JVKran/Taguino/Master/Boundary/HCSR04/main.cpp

#include "hwlib.hpp"
#include "HCSR04.hpp"

int main(){
   	auto triggerPin = hwlib::target::pin_out(hwlib::target::pins::d8);
   	auto echoPin = hwlib::target::pin_in(hwlib::target::pins::d9);
	auto distanceSensor = HCSR04(triggerPin, echoPin);

	//Wait for terminal
	hwlib::wait_ms(500);

	for(;;){
		hwlib::cout << "Distance: " << hwlib::setw(5) << distanceSensor.getDistance() << hwlib::endl;
		hwlib::wait_ms(1000);
	}
}
