JVKran/Taguino/Master/Boundary/Mp3/mp3.hpp

///@file
#ifndef _MP3_HPP
#define _MP3_HPP

#include <array>
#include "hwlib.hpp"
/// \brief
/// This sounds class has a template "<int, N>" and an array called sound where songs are put in.
/// \details
/// The Array holds N amount of ints, these ints are used to play a song.
/// This class has 3 functions:
///		- play(int i): 	The play function returns the given sound on its position.	
///		- size(): 		The size function returns the size of the sound array.
///		- set(): 		The set function sets the given value.

template< int N >
class sounds{
private:
	std::array< int, N > sound;
public:
/// \brief
/// Function to return from array sound.
/// \details
/// This function is used to return a value from sound at position i - 1.
	int play( int i ){ return sound[ i-1 ]; }
/// \brief
/// Function to return size of sound.
/// \details
/// This function returns the size of the sound array.
	int size(){ return sound.size();}
/// \brief
///	Function to set a sound.
/// \details
/// This function will set the given value at a new position.
	void set( int setSound ){ sound[setSound-1] = setSound; }

};

class hwuart{
	//Usart * hw_usart = USART0;
	public:
	hwuart();
	bool usart_char_available();
	char usart_getc();
	void usart_putc(char c);
};

/// \brief
///	The class send inherits from hwuart and is used to send commands to the mp3 module.
/// \details
///	The class has one function:
/// 	- executeCMD( uint8_t CMD, uint8_t par1, uint8_t par2): 
///     	This needs the mp3 command, command specific value, command specific value2 and will then send commands to the mp3 module.
class send : public hwuart{
public:
/// \brief
///	Function to execute commands to the mp3 module
/// \details
/// This needs the mp3 command, folder and mp3 file. It will send commands to the mp3 module.
	void executeCMD( uint8_t CMD, uint8_t par1, uint8_t par2);
};

/// \brief
///	The mp3 class inherits from send and is used to specify which commands need to be sent
/// \details
///	The class has 5 function:
/// 	- sendCMD(uint8_t CMD, uint8_t par1, uint8_t par2): Send your own commands.
/// 	- resetModule(): 			Reset the mp3 module.
/// 	- playSound( int sound ): 	Play the given sound.
/// 	- pauseSound(): 			Pause the sound.
/// 	- setVolume( int volume ): 	Set the volume.
class mp3 : public send{
public:
/// \brief
/// sendCMD sends your own commands.
/// \details
/// This function will send the command, command specific value, command specific value2 and executes it at the mp3 module.
	void sendCMD( uint8_t CMD, uint8_t par1, uint8_t par2 );
/// \brief
/// resetModule will reset the mp3 module.
/// \details
/// This function will send the command to reset to the mp3 module, 
/// clearing every command you have given to the module.
	void resetModule();
/// \brief
/// playSound will play the given sound.
/// \details
///	This function will send the command to play the given sound from the beginning.
/// Folders on the SD are numbered from 1-99 and mp3 files are numbered from 1 - 255, 
/// giving those values will play the corresponding sound. In this case the folder is always the first one.
	void playSound( int sound );
/// \brief
/// pauseSound will pause the current sound.
/// \details
/// This function will pause the sound that is currently playing,
/// altough there is no start function, meaning this can also be seen as stopping a sound.
	void pauseSound();
/// \brief
/// setVolume will set the volume at given value.
/// \details
/// This function will set the volume of the mp3 module at the given value,
/// the volume can go from 0 - 30.
	void setVolume( int volume ); //Van 0-30
};


/// \brief
/// The mp3Control class inherits mp3 and sounds<N>, it has a template "<int N>" and is used to play songs for given data in NRF
/// \details
/// This initializes the sound array and has 1 function:
/// 	- startPlayingSound(int data): If data is in the sound array, play it.

template< int N >
class mp3Control : public mp3, public sounds<N>{
private:
	int JAZZ=1; int ACTION=2; 
	std::array< int, N > soundTmp = { JAZZ, ACTION };
	sounds<N> sound;
public:
	mp3Control()
	{
		for( const auto &s : soundTmp){
			sound.set(s);
		}
	}
/// \brief
/// startPlayingSound will play a sound corresponding to the given data.
/// \details
/// This function will compare the data to the values in the array, if they are the same it will play the corresponding sound.
	void startPlayingSound( int data ){
		for( int i=1; i<sound.size()+1; i++){ 
			if( data == i ){ 			// If data is a song, play it. +1 because .play will return value -1;
				playSound( sound.play( i ) );
				break;
			}
		}
	}
};

#endif //MP3_HPP
