JVKran/Taguino/Master/Boundary/NRF/NRF24_register.hpp

// File      : NRF24_register.hpp
// Part of   : NRF24L01+ library
// Copyright : menno.vanderjagt@student.hu.nl 2019
//
// Distributed under the Boost Software License, Version 1.0.
// (See accompanying file LICENSE_1_0.txt or copy at 
// http://www.boost.org/LICENSE_1_0.txt)

//commando's
#define R_REGISTER           0x00        //Leest commando en status registers, 5 bit register map address
#define W_REGISTER           0x20        //Schrijft commando en status registers, 5 bit register map address. Uitvoerbaar in power down
#define R_RX_PAYLOAD         0x61        //Leest de RX-payload: 1 - 32 bytes
#define W_TX_PAYLOAD         0xA0        //Schrijft TX-payload 1 - 32 bytes
#define FLUSH_TX             0xE1        //Flush TX FIFO, in TX mode
#define FLUSH_RX             0xE2        //Flush RX FIFO, in RX mode
#define REUSE_TX_PL          0xE3        //Wordt gebruikt voor PTX apparaten, hergebruik laatst verstuurde payload
#define R_RX_PL_WID          0x60        //Leest RX payload wijdte
#define W_ACK_PAYLOAD        0xA8        //Schrijft payload om met ACK packet te worden verstuurd
#define W_TX_PAYLOAD_NOACK   0xB0        //Zet AUTOACK uit voor een specifiek packet
#define NOP                  0xFF        //Geen operatie, kan gebruikt worden om het STATUS register te lezen

//addresses
#define CONFIG               0x00        //Configuration register
#define EN_AA                0x01        //Enable 'Auto Acknowledgment' function
#define EN_RXADDR            0x02        //Enabled RX Addresses
#define SETUP_AW             0x03        //Setup of address widths
#define SETUP_RETR           0x04        //Setup of automatic retransmission
#define RF_CH                0x05        //RF channel (sets the frequency channel where nRF is operation on)
#define RF_SETUP             0x06        //RF setup register
#define STATUS               0x07        //Status register
#define OBSERVE_TX           0x08        //Transmit observe register
#define RPD                  0x09        //no information available
#define RX_ADDR_P0           0x0A        //Receive address data pipe 0, maximum 5 bytes length
#define RX_ADDR_P1           0x0B        //Receive address data pipe 1, maximum 5 bytes length
#define RX_ADDR_P2           0x0C        //Receive address data pipe 2, maximum 5 bytes length
#define RX_ADDR_P3           0x0D        //Receive address data pipe 3, maximum 5 bytes length
#define RX_ADDR_P4           0x0E        //Receive address data pipe 4, maximum 5 bytes length
#define RX_ADDR_P5           0x0F        //Receive address data pipe 5, maximum 5 bytes length
#define TX_ADDR              0x10        //Transmit address. Used for a PTX device only 
#define RX_PW_P0             0x11        
#define RX_PW_P1             0x12           
#define RX_PW_P2             0x13
#define RX_PW_P3             0x14
#define RX_PW_P4             0x15
#define RX_PW_P5             0x16
#define FIFO_STATUS          0x17        //FIFO status register
#define DYNPD                0x1C        //Enable dynamic payload length
#define FEATURE              0x1D        //Feature register

//mnemonic
#define MASK_RX_DR           6        //Mask interrupt caused by RX_DR
#define MASK_TX_DS           5        //Mask interrupt caused by TX-DS
#define MASK_MAX_RT          4        //Mask interrupt caused by MAX_RT
#define EN_CRC               3        //Enable CRC. Forced high if one of the bits in the EN_AA is high
#define CRCO                 2        //CRC encoding scheme
#define PWR_UP               1        //1: POWER UP, 0: POWER DOWN
#define PRIM_RX              0        //1: PRX, 0: PTX
#define ENAA_P5              5        //Enable auto acknowledgment data pipe 5    
#define ENAA_P4              4        //Enable auto acknowledgment data pipe 4
#define ENAA_P3              3        //Enable auto acknowledgment data pipe 3
#define ENAA_P2              2        //Enable auto acknowledgment data pipe 2
#define ENAA_P1              1        //Enable auto acknowledgment data pipe 1
#define ENAA_P0              0        //Enable auto acknowledgment data pipe 0
#define ERX_P5               5        //Enable data pipe 5
#define ERX_P4               4        //Enable data pipe 4
#define ERX_P3               3        //Enable data pipe 3
#define ERX_P2               2        //Enable data pipe 2
#define ERX_P1               1        //Enable data pipe 1
#define ERX_P0               0        //Enable data pipe 0
#define AW                   0        //RX/TX address field width '00' - illegal, '01' - 3 bytes, '10' - 4 bytes, '11' - 5 bytes
#define ARD                  4        //Auto Retransmit Delay
#define ARC                  0        //Auto Retransmit Count
#define CONT_WAVE            7        //Enables continuous carrier trasmit when high
#define RF_DR_LOW            5        //Set RF data rate to 250kps
#define PLL_LOCK             4        //Force PLL lock signal (only used in test)
#define RF_DR_HIGH           3        //Select between the high speed data rates
#define RF_PWR_LOW           1        //Set RF output power low
#define RF_PWR_HIGH          2        //Set RF output power high
#define RX_DR                6        //Data ready RX FIFO interrupt     
#define TX_DS                5        //Data sent TX FIFO interrupt
#define MAX_RT               4        //Maximum number of TX retransmits interrupt 
#define RX_P_NO              1        //Data pipe number for the payload available for reading from RX_FIFO
#define PLOS_CNT             4        //Count lost packets
#define ARC_CNT              0        //Count retransmitted packets
#define TX_REUSE             6        //Used for a PTX device
#define TX_FULL              5        //TX FIFO full flag, 1: TX FIFO full, 0: Available locations in TX FIFO
#define TX_EMPTY             4        //TX FIFO empty flag, 1: TX FIFO empty, 0: Data in TX FIFO
#define RX_FULL              1        //RX FIFO full flag, 1: RX FIFO full, 0: Available locations in RX FIFO
#define RX_EMPTY             0        //RX FIFO empty flag, 1: RX FIFO empty, 0: Data in RX FIFO
#define DPL_P5               5        //Enable dynamic payload length data pipe 5
#define DPL_P4               4        //Enable dynamic payload length data pipe 4
#define DPL_P3               3        //Enable dynamic payload length data pipe 3
#define DPL_P2               2        //Enable dynamic payload length data pipe 2
#define DPL_P1               1        //Enable dynamic payload length data pipe 1
#define DPL_P0               0        //Enable dynamic payload length data pipe 0
#define EN_DPL               2        //Enables dynamic payload length
#define EN_ACK_PAY           1        //Enables payload with ACK
#define EN_DYN_ACK           0        //Enables the W_RX_PAYLOAD_NOACK command
