JVKran/Taguino/Weapon/Boundary/RGBLed/RGBLed.hpp

/// @file

#ifndef __RGB_LED_HPP
#define __RGB_LED_HPP

/// \brief
/// RGB Led
/// \details
/// This class is responsible for giving leds another color.
class RGBLed{
private:
    hwlib::color currentcolor;
    uint32_t mask;
public:
	RGBLed(hwlib::color color = hwlib::color(0, 0, 0));
    void setColor(hwlib::color color);
};


#endif //__RGB_LED_HPP
