JVKran/Taguino/Master/Control/signup.cpp

/// @file

#include "signup.hpp"


/// \brief
/// Constructor
/// \details
/// Starts Lobby music to join game.
signUp::signUp(NRF24 & radio, inputHandler &handler, game &Game,scoreboard &board, display & Display):
	radio(radio),
	Display(Display),
	toetsenbord(this),
	Game(Game),
	board(board)


	{
		mp3Player.startPlayingSound(1); // Start lobby music once.
		handler.addkeypad(&toetsenbord);
		for(auto & element : name){
			element = 0;
		}
	}

/// \brief
/// Data Received
/// \details
/// Gets called when data is received
void signUp::dataReceived(const uint8_t data[10], const int len){
	if(data[0] == 1){
		if(assignedWeapons < 31){
			hwlib::cout << "Weapon turned on. Gave him address ";
			radio.powerDown_rx();
			transmitAddress[4] = 100;
			radio.write_pipe( transmitAddress );
			dataToTransmit[0] = 8;					//8 is defined as newScoreMessage
			dataToTransmit[1] = assignedWeapons;
			for(unsigned int i = 0; i < 2; i++){
				radio.write( dataToTransmit, amountOfDataToTransmit );
				hwlib::wait_ms(100);
			}
			hwlib::cout << assignedWeapons << "." << hwlib::endl;
			radio.write( dataToTransmit, amountOfDataToTransmit );
			radio.read_pipe(receiveAddress);
			radio.powerUp_rx();
			assignedWeapons++;
		}
	}
}

/// \brief
/// Key Pressed
/// \details
/// Gets called when a key is pressed.
void signUp::keyPressed(char karakter){
	if(karakter == 'I' || namePos == 7){
		hwlib::cout << "Name Entered: ";
		for(int i=0; i<namePos; i++){
			board.playerNames[assignedNames][i] = name[i];
			hwlib::cout << board.playerNames[assignedNames][i];
		}
		hwlib::cout << hwlib::endl;
		for(auto & element : name){
			element = 0;
		}
		namePos = 0;
		assignedNames++;
	} else if(karakter == '4'){
		namePos--;
		name[namePos] = 0;
	} else {
		name[namePos]= karakter;
		namePos++;
	}
	Display.nameEntered(name);
}

/// \brief
/// StartGame
/// \details
/// Starts Game for all online weapons based on protocol as defined in documentation.
void signUp::startGame(const uint8_t gameTime){
	Game.gamestarted =1;
	mp3Player.startPlayingSound(2);	// Start action music once.
	
	radio.powerDown_rx();
	hwlib::wait_ms(1000);
	hwlib::cout << "Started game for players ";
	for(uint8_t i = 1; i < assignedWeapons; i++){
		hwlib::cout << i << " ";
	}
	hwlib::cout << " and " << assignedWeapons << hwlib::endl;
	for(uint8_t i = 1; i < assignedWeapons; i++){		//Transmit start message 3 times.

		for(uint8_t j = 0; j < 3; j++){	
			hwlib::cout<<"start"<<i<<"poging  "<<j<<"met tijd"<<Game.getGameTime()<<hwlib::endl;								

			transmitAddress[4] = i;
			radio.write_pipe( transmitAddress );
			dataToTransmit[0] = 1;						//2 is defined as newScoreMessage.
			dataToTransmit[1] = Game.getGameTime();
			radio.write( dataToTransmit, amountOfDataToTransmit );
			hwlib::wait_ms(100);
		}
	}
	radio.read_pipe(receiveAddress);
	radio.powerUp_rx();

}
