JVKran/Taguino/Master/Boundary/keypadtask/keypad.cpp

#include "keypad.hpp"

T9Keys::T9Keys(keypadListener* listen):
    listen(listen)
{}

void T9Keys::update(){
        if(((hwlib::now_us()-lastpress) > 1000000)&&returned==false){
            listen->keyPressed(karakter);
            returned=true;
 
        }
        else{
        if(numpad.char_available()){
            //hwlib::wait_ms(10);
            if((hwlib::now_us()-lastpress) > 1000000){
                returned= false;
                count=0;

                
                i=numpad.getc();
                lastpress=hwlib::now_us();
                if(i=='7'){
                    multiplier=0;
                    maxcount= 3;
                }
                else if(i =='8'){
                    maxcount=2;
                    multiplier=1;
                }
                else if(i=='9')
                {
                    multiplier=1;
                    maxcount=3;
                }
                
                else
                {
                    maxcount=2;
                    multiplier=0;
                }
                if(int(i)>0){
                    karakter= (((i - '0') - 2) * 3) + 97+multiplier;
                    //hwlib::cout<<karakter<<hwlib::endl;
                }
        }
        else
        {
            //hwlib::wait_ms(10);

            if((numpad.getc()==i)&&(count<maxcount)){
                count++;
                karakter+=1;
                //hwlib::cout<<karakter<<hwlib::endl;

            }
            else{
                lastpress=0;
            }
        



        }
        }
    }
    }
        
        

//}




char T9Keys::readChar(){
    return 0;
}

/// \brief
/// Read Key
/// \details
/// This function returns the character of the pressed key equal to the one drawn on the numpad.
char T9Keys::readKey(){
	return numpad.pressed();
}

/// \brief
/// Debug
/// \details
/// This function can be used for debugging. It prints the amount of presses that have been done
/// and the pressed key.
void T9Keys::debug(){
   	int n = 0;
   	for(;;){
	   	if(numpad.char_available()){
	   		hwlib::cout << n++ << " [" << numpad.getc() << "]\n";
	   	}
   	}
}
