JVKran/Taguino/Master/Boundary/buttoninterrupt/button.hpp

#ifndef __BUTTON_INTERRUPTER_HPP
#define __BUTTON_INTERRUPTER_HPP


class Buttoninterrupter{
private:
    uint32_t registercont;
    uint32_t mask;
    uint32_t mask2;




public:
    void refreshregister();            //store a copy of the register content, needed because the register clears on read
    bool read(uint8_t pin);           //read the stored copy of the interrupt register for pin i

    Buttoninterrupter();           // constructor


};

class rotaryEncoder{
    public:
    int32_t read();
    rotaryEncoder();
};

#endif //__BUTTON_INTERRUPTER_HPP
